mpvano/LPF2/txfilters21/5bandFilters/80M.asc

C1: cap; 470p
C3: cap; 1200p
C5: cap; 1200p
C7: cap; 470p
L2: ind; 2.42µ; Rser=1
L4: ind; 3.01µ; Rser=1
L6: ind; 2.42µ; Rser=1
RL: res; 50
V1: voltage; ""; AC 1 0; Rser=50.00
Named nets: 0
.ac dec 1001 1.0Meg 50.00Meg
.net I(RL) V1
7th Order Chebyshev Lowpass
Shunt First
Cutoff Frequency = 4.0 MHz
Passband Ripple = 0.10 dB

rf-tools.com | Feb 21 2024 16:04
Inductor Q Factor = 30 at 14.50MHz
